mattywausb/lightstick/docs/circuit.jpg

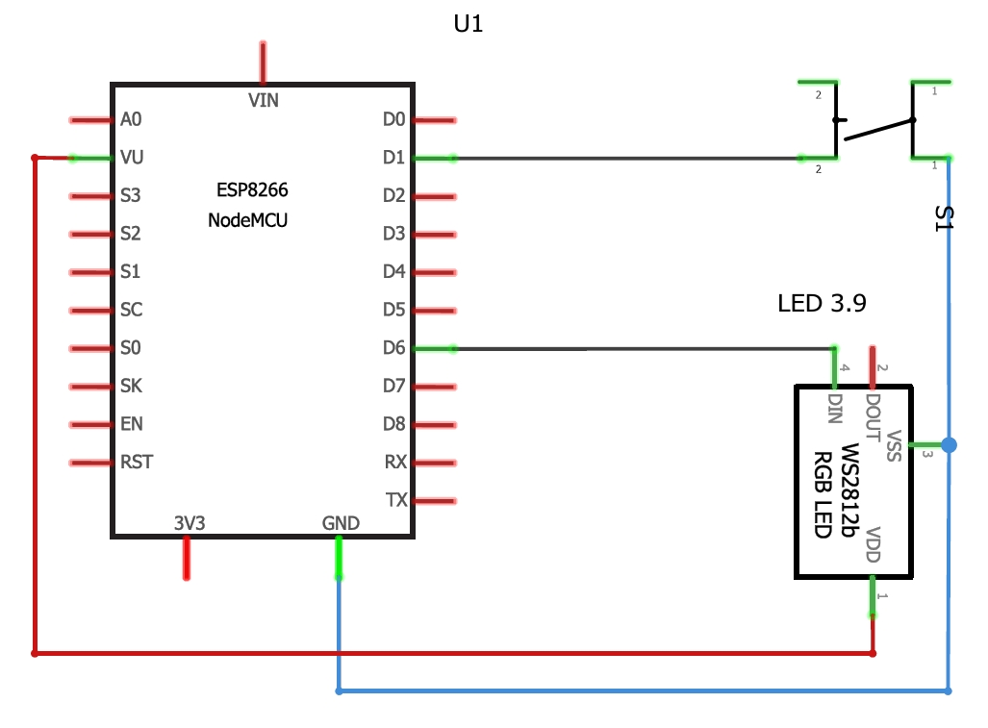
docs/circuit.jpg
