mattywausb/lightstick/docs/D1_mini_pcb_back.jpg

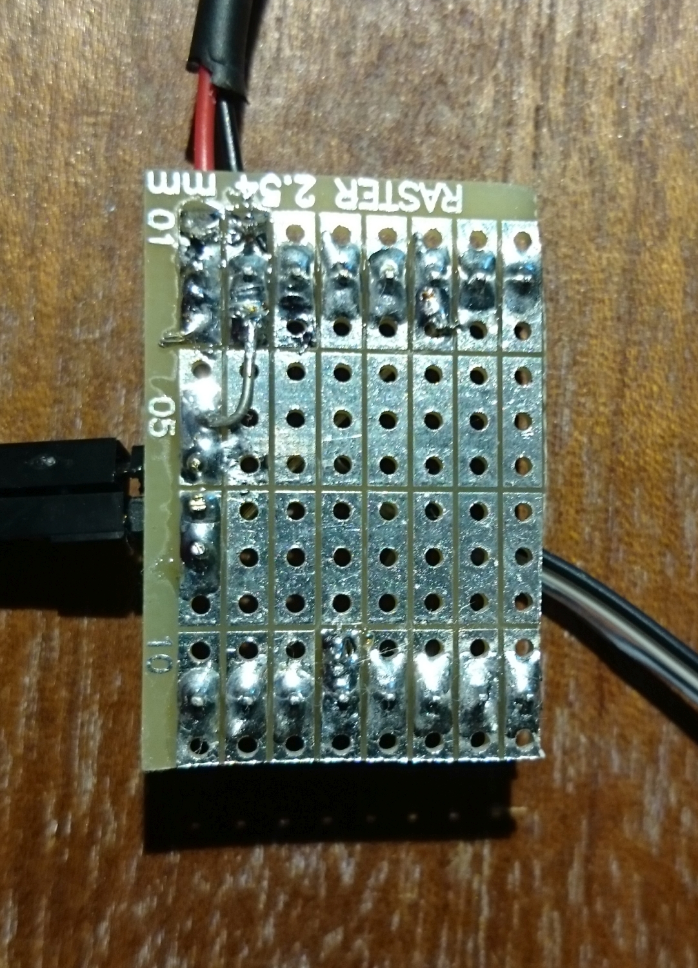
docs/D1_mini_pcb_back.jpg
