mattywausb/lightstick/docs/D1_mini_full_setup.jpg

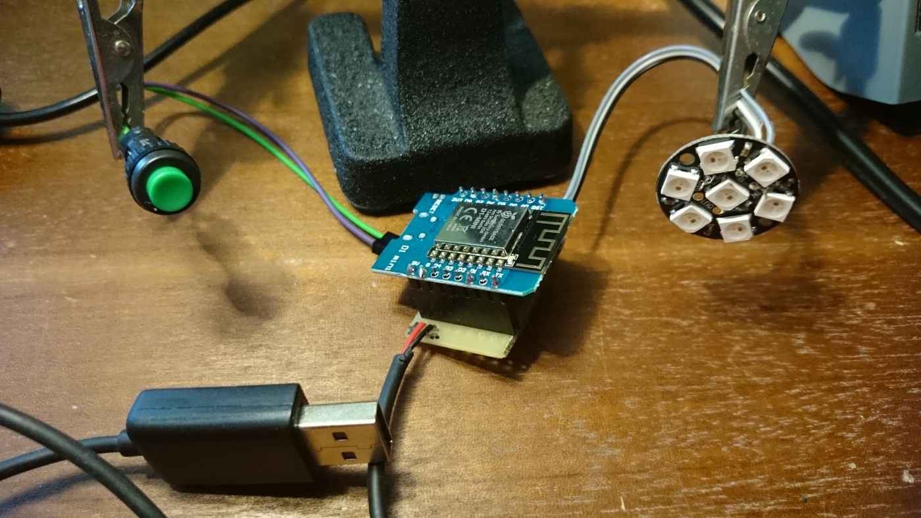
docs/D1_mini_full_setup.jpg
