mattywausb/lightstick/docs/Head_assembly_2.jpg

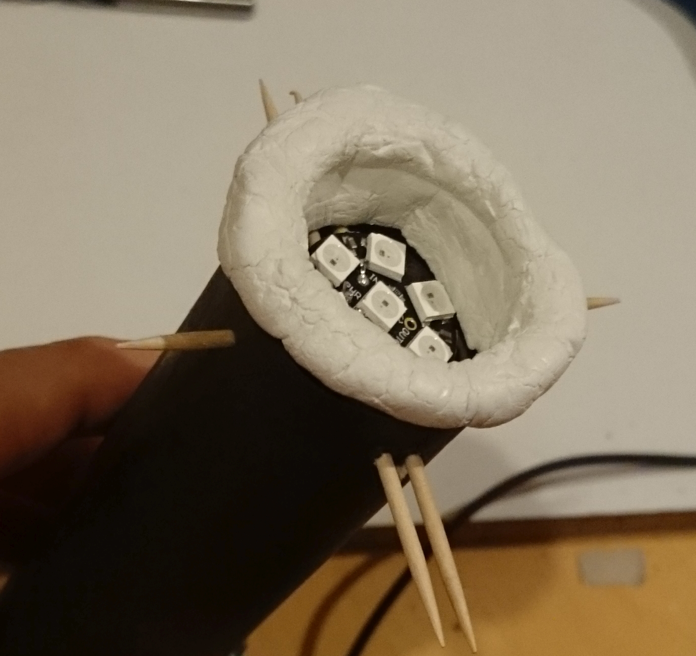
docs/Head_assembly_2.jpg
