mattywausb/lightstick/docs/Head_assembly_3.jpg

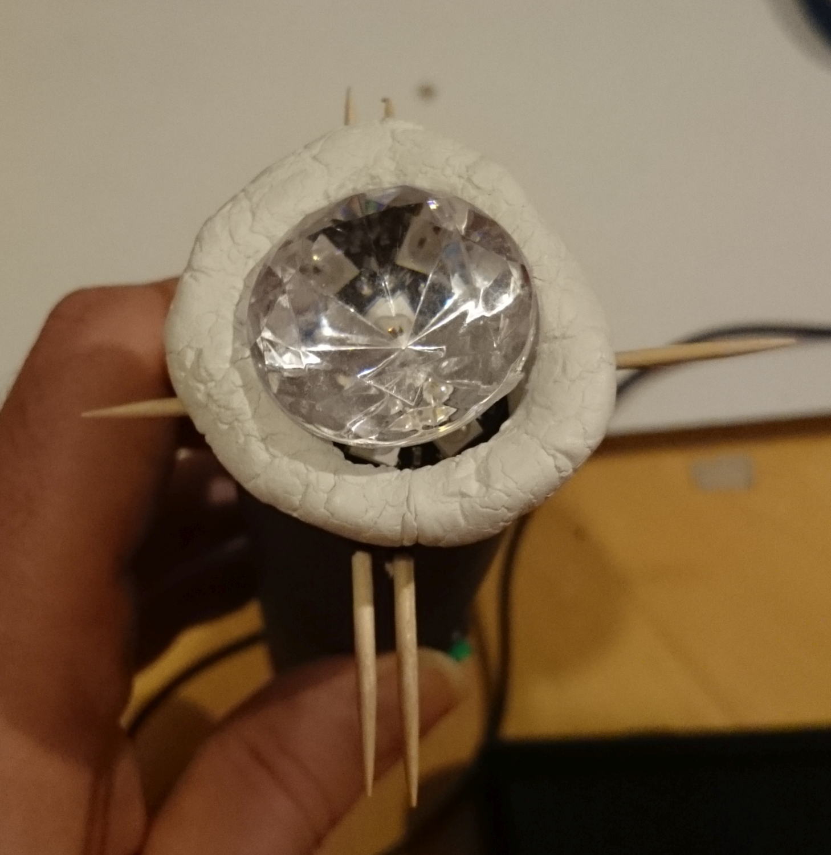
docs/Head_assembly_3.jpg
