mattywausb/lightstick/docs/lightstick_build_schematics.png

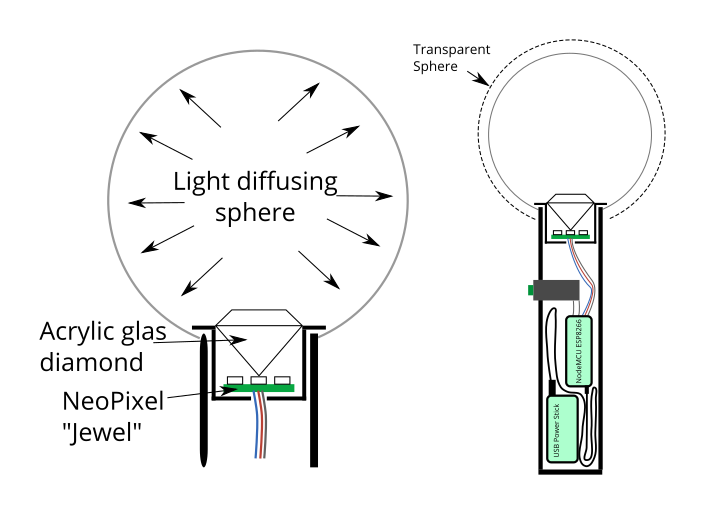
docs/lightstick_build_schematics.png
