mattywausb/lightstick/the_light_stick/webui.ino

/* Compile against  NodeMCU 1.0 Profile */

/*
 * Demonstrate using an http server and an HTML form to control an LED.
 * The http server runs on the ESP8266.
 *
 * Connect to "http://esp8266WebForm.local" or "http://<IP address>"
 * to bring up an HTML form to control the LED connected GPIO#0. This works
 * for the Adafruit ESP8266 HUZZAH but the LED may be on a different pin on
 * other breakout boards.
 *
 * Imperatives to turn the LED on/off using a non-browser http client.
 * For example, using wget.
 * $ wget http://esp8266webform.local/ledon
 * $ wget http://esp8266webform.local/ledoff
*/

#include <ESP8266WiFi.h>
#include <WiFiClient.h>
#include <ESP8266WebServer.h>
#include <ESP8266mDNS.h>
#include "wifi_credentials.h"
#include "webui.h"
#include "mainSettings.h"
#include "lamp.h"

#ifdef TRACE_ON
#define TR_WEBUI
//#define TR_WEBUI_PAGE_GENERATION
#define TR_WEBUI_CONNECT
#endif

/* Macro to declare Strings with reserved buffer */
#define DECLARE_PREALLOCATED_STRING(varname, alloc_size) String varname((const char*)nullptr); varname.reserve(alloc_size)

#define MAX_DEFINITON_STRING_LENGTH 150

//  SSID and password are defined in header file that will not be in the git repo
const char* ssid = STASSID;
const char* password = STAPSK;

String webui_ssid_input="";
String webui_password_input="";
IPAddress webui_ipAddress(0,0,0,0);

t_webui_connect_mode webui_connect_mode =NONE; 

MDNSResponder mdns;

ESP8266WebServer server(80);

String softAp_password="letsparty";

String webui_hostname="lighstick";


/* HTML Header */ 

const char WEB_PAGE_HEADER[] PROGMEM = "<!DOCTYPE html><html>"
"<head> <title>Lightstick</title> "
"<meta http-equiv=\"content-type\" content=\"text/html; charset=utf-8\">"
"<meta name=\"viewport\" content=\"width = device-width, initial-scale = 1.0, maximum-scale = 1.0, user-scalable=0\">"
"<link href=\"default.css\" rel=\"stylesheet\" type=\"text/css\">"
"</head><body>";

const char TXT_CONTENT_TYPE_TEXT_HTML[] PROGMEM = "text/html; charset=utf-8";

void sendStylesheet() {
    #ifdef TR_WEBUI
    Serial.println(F("TR_WEBUI> Sending Stylesheet "));
  #endif
   server.send(200, "text/css", F(
"body{font-family:\"OpenSans\",\"Arial\",\"mono\";color:#f7d53d;background-color:#193c3d;font-size:16px ;text-align:left;}"
"h1{margin:2px 2px ;font-size:18px ;padding:2px 2px ;}"
"label{float:left;margin:2px 2px ;font-size:18px ;padding:2px 2px ;}"
"input[type=\"submit\"]{background-color:#773172;border-radius:4px ;border:none;color:#f7d53d;margin:2px 2px ;padding:16px 16px ;font-size:16px ;cursor:pointer; width:100%}"
"input[type=\"submit\"]:hover{background-color:#a6449f;color:#fff;}"
"input{background-color:#317577;border-radius:4px ;border:none;color:#f7d53d;box-sizing:border-box;margin:2px 2px ;padding:10px 10px ;}"
"select{background-color:#317577;border-radius:4px;border:none;color:#f7d53d;box-sizing:border-box;margin:2px 2px;padding:10px 10px;}"
"textarea{background-color:#317577;border-radius:4px ;border:none;color:#f7d53d;box-sizing:border-box;margin:2px 2px ;padding:10px 10px ;}"
".lb{display:block;background-color:#773172;border-radius:4px ;border:none;color:#f7d53d;padding:10px 10px ;font-size:14px ;cursor:pointer;text-decoration:none}"
".lb:hover{background-color:#a6449f;color:#fff;}"
".lb_box{padding:2px 2px;}"
".anntn{font-size:10px;margin:2px 2px;}"));
}

/* Switchgrid constants */
const char pattx_disco[] PROGMEM ="Disco";
const char pattx_flat[] PROGMEM ="Flat";
const char pattx_orbit[] PROGMEM ="Orbit";
const char pattx_pulse[] PROGMEM ="Pulse";
const char pattx_quater[] PROGMEM ="Quater";
const char pattx_rainbow[] PROGMEM ="Rainbow";
const char pattx_sparkle[] PROGMEM ="Sparkle";
const char pattx_wave[] PROGMEM ="Wave";
const char pattx_whipe[] PROGMEM ="Whipe";

typedef struct pattern_button {
  const char *label;
  int   pattern_id;
  int base_speed;
} t_pattern_button;

t_pattern_button webui_pattern_button[] {
  {pattx_pulse,2,4},    {pattx_whipe,10,4},   {pattx_wave,11,8},
  {pattx_orbit,24,8},   {pattx_disco,44,4},   {pattx_sparkle,104,16},
  {pattx_rainbow,60,16}, {pattx_quater,80,16},  {pattx_flat,90,2}
};

#define WEBUI_PATTERN_BUTTON_COUNT 9


const char coltx_blue[] PROGMEM ="Blue";
const char coltx_cyan[] PROGMEM ="Cyan";
const char coltx_green[] PROGMEM ="Green";
const char coltx_lemon[] PROGMEM ="Lemon";
const char coltx_orange[] PROGMEM ="Orange";
const char coltx_pink[] PROGMEM ="Pink";
const char coltx_purple[] PROGMEM ="Purple";
const char coltx_red[] PROGMEM ="Red";
const char coltx_rose[] PROGMEM ="Rose";
const char coltx_sky[] PROGMEM ="Sky";
const char coltx_white[] PROGMEM ="White";
const char coltx_yellow[] PROGMEM ="Yellow";


typedef struct color_button {
  const char *label;
  int hue;
  float saturation;
} t_color_button;

t_color_button webui_color_button [] {
  {coltx_pink,HUE_PINK,1.0},      {coltx_red,HUE_RED,1.0},    {coltx_orange,HUE_ORANGE,1.0},
  {coltx_yellow, HUE_YELLOW,1.0}, {coltx_lemon,HUE_LEMON,1.0},{coltx_green,HUE_GREEN,1.0} ,
  {coltx_cyan,HUE_CYAN,1.0},      {coltx_sky,HUE_SKYBLUE,1.0},   {coltx_blue,HUE_BLUE,1.0} ,
  {coltx_purple, HUE_PURPLE,1.0} ,{coltx_rose, HUE_RED,SAT_ROSE} ,{coltx_white,HUE_ORANGE,0.0}
};

#define WEBUI_COLOR_BUTTON_COUNT 12




static void send_html_header() {
 
  DECLARE_PREALLOCATED_STRING(s, LARGE_STR);
  s = FPSTR(WEB_PAGE_HEADER);
  server.setContentLength(CONTENT_LENGTH_UNKNOWN);
  server.send(200, FPSTR(TXT_CONTENT_TYPE_TEXT_HTML), s);
}

/* End of Webpage */
const char WEB_PAGE_FOOTER[] PROGMEM = "<hr><div class=\"anntn\">Firmware Build " __DATE__ " " __TIME__ "</div> </body></html>\r\n";


static void send_html_footer() {
  server.sendContent_P(WEB_PAGE_FOOTER);
  #ifdef TR_WEBUI
    Serial.println(F("TR_WEBUI> Page sent "));
  #endif
      
}

const char WEB_PAGE_BUTTON_TABLE_START[] PROGMEM =
      "<div>" 
      "<table width=100%>";
      
const char WEB_PAGE_PATTERN_PART_HEADING[] PROGMEM =
      "<tr>"
      "<td><h1>Pattern</h1></td>"
      "</tr>"; 

const char WEB_PAGE_COLOR_PART_HEADING[] PROGMEM =
      "<tr>"
      "<td><h1>Color<h1></td>"
      "</tr>"; 

const char WEB_PAGE_BUTTON_TABLE_END[] PROGMEM = "</table></div>";


const char WEB_PAGE_FORM_SECTION_START[] PROGMEM ="<hr/><div><form id=\"progform\" action=\"/#progform\" method=\"post\">"; 

const char WEB_PAGE_SEQ_PART_START[] PROGMEM =
      "<div> <label for=\"Sequence\" >Song Sequence</label>"
      "<textarea  id=\"Sequence\" name=\"Sequence\" style=\"width:100%; height:3;\" >";
  

const char WEB_PAGE_SEQ_PART_END[] PROGMEM =
      "</textarea> </div>"
      "<div class=\"anntn\">"
      "Syntax: &lt;bpm&gt; &lt;Part Letter&gt; &lt;Beats&gt;&lt;Beats&gt;... &lt;Part Letter&gt;...<br/>"
      "# = Forward immediatly to next on button press <br/>"
      "&gt; = Jump back here after end<br/>"
      "Part Letter is defined in Song part configuration<br/>"
      "Beats are one digit numbers, that get accumulated: 8888=32 Beats <br/>"
      "248 =14 Beats"
      "</div>";

const char WEB_PAGE_SONG_PART_START[] PROGMEM =
      "<div > <label for=\"Parts\" >Song Parts</label>"
      "<textarea  id=\"Parts\" name=\"Parts\" style=\"width:100%; height:1; \" >";

const char WEB_PAGE_SONG_PART_END[] PROGMEM =
      "</textarea> </div>"
      "<div class=\"anntn\">"
      "Syntax:  &lt;Part Letter&gt;&lt;Pattern&gt;/&lt;Speed&gt;:&lt;color&gt;... <br/>"
      "Pattern: identifies the pattern of light change (see pattern catalog)<br/>"
      "Speed: Speed of the pattern 2=Haft Beat 4=Beat 8=8th, 16,32,64 <br/>"
      "Color: defines the color palette (see color catalog)"
      "</div>";

const char WEB_PAGE_FORM_END[] PROGMEM =
      "<input type=\"submit\" value=\"Start\">"
      "</form>";

const char WEB_PRESET_SECTION_START[] PROGMEM =
      "<hr/>"
      "<h1 id=\"presets\">Song Presets</h1>";

const char WEB_FILEFORM_P1[] PROGMEM =
      "<hr/>"
      "<form id=\"fileform\" action=\"#fileform\" method=\"post\">"
      "<table width=100%>"
      "<tr><td><label for=\"filename\" >Filename</label>"
      "<input type=\"text\" id=\"filename\" name=\"filename\" value=\"";
      // Insert Filename here
const char WEB_FILEFORM_P2[] PROGMEM =
      "\">"
      "</td><td><label for=\"file-op\">Operation</label>"
      "<select id=\"file-op\" name=\"file-op\">"
        "<option value=\"cre\">create</option>"
        "<option value=\"upd\">update</option>"
        "<option value=\"del\">delete</option>"
      "</select>"
      "</td><td ><div style=\"color:#ff0000\" ><b>";
      // Insert catalog message here
const char WEB_FILEFORM_P3[] PROGMEM =
      "</b></div>"
      "</td></tr></table>"
      "<input type=\"submit\" value=\"Execute\">"
      "</form>";

const char WEB_WIFI_P1[] PROGMEM =
          "<hr/>"
          "<h1>Wifi Settings</h1>"
          "<form action=\"/\" method=\"post\">"
          "<table><tr>"
          "<td><label for=\"SSID\" class=\"col-1\">SSID</label>"
          "<input type=\"text\" id=\"SSID\" name=\"SSID\" value=\"";
          // Insert SSID String 
const char WEB_WIFI_P2[] PROGMEM =
          "\"></td>"
          "<td><label for=\"Password\" class=\"col-1\">Password</label>"
          "<input type=\"text\" id=\"WIFIPW\" name=\"WIFIPW\" value=\"";
          // Insert wifi password here
const char WEB_WIFI_P3[] PROGMEM =
        "\" autocomplete=\"off\" autocapitalize=\"off\" autocorrect=\"off\"></td>"
         "</table></tr>"
        "<div class=\"anntn\" >"
        "To try out the credentials, the stick will disconnect and this website will not be available any more. When successfull, access the stick in the target network. In case of blue light, connect to the sticks own wifi to access it"
        "</div>"
        "<input type=\"submit\" value=\"connect to wifi\">"
        "</form>";

         
      

void send_main_page() {

  #ifdef TR_WEBUI
   Serial.println(F("TR_WEBUI> send_main_page started"));
  #endif
  
  String local_buffer_string;
  
  send_html_header() ;

  char string_buffer[MAX_DEFINITON_STRING_LENGTH];
  
  DECLARE_PREALLOCATED_STRING(content_element,XLARGE_STR);
  
  // *******************  Button Grid ***************************
  server.sendContent_P(WEB_PAGE_BUTTON_TABLE_START);

  // -------------- Pattern Buttons ------------------------
  #ifdef TR_WEBUI_PAGE_GENERATION
   Serial.println(F("TR_WEBUI_PAGE_GENERATION> render pattern buttons"));
  #endif
    server.sendContent_P(WEB_PAGE_PATTERN_PART_HEADING);
    for(int element_index=0;element_index<WEBUI_PATTERN_BUTTON_COUNT;element_index++) {
        if(element_index%3==0) content_element+="<tr>"; 

        content_element+=F("<td><div class=\"lb_box\"><a class=\"lb\"  href=\"/switch?p=");
        content_element+=webui_pattern_button[element_index].pattern_id;
        content_element+=F("&w=");
        content_element+=webui_pattern_button[element_index].base_speed;
        content_element+=("\">");
        strcpy_P(string_buffer, (char*)pgm_read_dword(&(webui_pattern_button[element_index].label)));
        content_element+=string_buffer;
        content_element+=F("</a></div></td>");
    
        content_element+=F("<td><div class=\"lb_box\"><a class=\"lb\"  href=\"/switch?p=");
        content_element+=webui_pattern_button[element_index].pattern_id;
        content_element+=F("&w=");
        content_element+=webui_pattern_button[element_index].base_speed*4;
        content_element+=("\">&gt;&gt;");
        content_element+=F("</a></div></td>");
        if(element_index%3==2) content_element+="</tr>";  // Works only for button count  that is dividable by 3
   } // end loop over all Pattern Buttons
   server.sendContent(content_element);
   content_element="";
   
  // -------------- color Buttons ------------------------
  #ifdef TR_WEBUI_PAGE_GENERATION
   Serial.println(F("TR_WEBUI_PAGE_GENERATION> render color buttons"));
  #endif
    server.sendContent_P(WEB_PAGE_COLOR_PART_HEADING);
    
    for(int element_index=0;element_index<WEBUI_COLOR_BUTTON_COUNT;element_index++) {
        if(element_index%3==0) content_element+="<tr>"; // 3 Column format
        content_element+=F("<td><div class=\"lb_box\"><a class=\"lb\"  href=\"/switch?i=1&h=");
        content_element+=webui_color_button[element_index].hue;
        content_element+=F("&s=");
        content_element+=webui_color_button[element_index].saturation;
        content_element+="\">";
        strcpy_P(string_buffer, (char*)pgm_read_dword(&(webui_color_button[element_index].label)));
        content_element+=string_buffer;
        content_element+=F("</a></div></td>");
        content_element+=F("<td><div class=\"lb_box\"><a class=\"lb\"  href=\"/switch?h=");
        content_element+=webui_color_button[element_index].hue;
        content_element+=F("&s=");
        content_element+=webui_color_button[element_index].saturation;
        content_element+="\">+";
        content_element+=F("</a></div></td>");
        if(element_index%3==2) content_element+="</tr>";  // Works only for button count that is dividable by 3
      }
   server.sendContent(content_element);
   content_element="";
   server.sendContent_P(WEB_PAGE_BUTTON_TABLE_END);
 
  // *******************Song catalog ****************
  #ifdef TR_WEBUI_PAGE_GENERATION
   Serial.println(F("TR_WEBUI_PAGE_GENERATION> render song preset buttons"));
  #endif
 
  server.sendContent_P(WEB_PRESET_SECTION_START);
  song_catalog_goto_start();
  while(song_catalog_next()) {
        local_buffer_string=song_catalog_list_name;
        local_buffer_string.replace(" ","_");
        content_element+=F("<div class=\"lb_box\"><a class=\"lb\"  href=\"song?song_name=");
        content_element+=(local_buffer_string);  
        content_element+=F("#presets\">");
        content_element+=song_catalog_list_name;
        content_element+=F("</a></div>");
  } // Loop over song catalog

  /*Now get it all out to the user */
  server.sendContent(content_element);

  // ******************* Send Sequence Section Form ****************
  #ifdef TR_WEBUI_PAGE_GENERATION
   Serial.println(F("TR_WEBUI_PAGE_GENERATION> render seqence entry form"));
  #endif
  
  server.sendContent_P(WEB_PAGE_FORM_SECTION_START);

  // Parts
  server.sendContent_P(WEB_PAGE_SONG_PART_START);
  if(song_catalog_current_parts.length()>0) server.sendContent(song_catalog_current_parts);
  server.sendContent_P(WEB_PAGE_SONG_PART_END);

  // Sequence
  server.sendContent_P(WEB_PAGE_SEQ_PART_START);
  if(song_catalog_current_sequence.length()>0) server.sendContent(song_catalog_current_sequence);
  server.sendContent_P(WEB_PAGE_SEQ_PART_END);
  
  // End of Part/ Sequence Form
  server.sendContent_P(WEB_PAGE_FORM_END);

  // ******************* Send file management form ****************
  #ifdef TR_WEBUI_PAGE_GENERATION
   Serial.println(F("TR_WEBUI_PAGE_GENERATION> render file management form"));
  #endif

  server.sendContent_P(WEB_FILEFORM_P1);
  if(song_catalog_current_name.length()>0) server.sendContent(song_catalog_current_name);
  server.sendContent_P(WEB_FILEFORM_P2);
  if(song_catalog_status_message.length()>0) server.sendContent(song_catalog_status_message);
  song_catalog_status_message="";
  server.sendContent_P(WEB_FILEFORM_P3);

  // ******************* Wifi connect form ****************
  #ifdef TR_WEBUI_PAGE_GENERATION
   Serial.println(F("TR_WEBUI_PAGE_GENERATION> render wifi connect form"));
  #endif

  server.sendContent_P(WEB_WIFI_P1);
  if(webui_ssid_input.length()>0) server.sendContent(webui_ssid_input);
  server.sendContent_P(WEB_WIFI_P2);
  if(webui_password_input.length()>0) server.sendContent(webui_password_input);
  server.sendContent_P(WEB_WIFI_P3);
 
  // ******************* finally  ****************
  #ifdef TR_WEBUI_PAGE_GENERATION
   Serial.println(F("TR_WEBUI_PAGE_GENERATION> html render complete"));
  #endif
  send_html_footer();
}

// ************* Request management FORMS ****************************

void receiveSongConfigForm()
{
  #ifdef TR_WEBUI
    Serial.println(F("TR_WEBUI> receiveSongConfigForm started"));
  #endif
  if (server.hasArg("Parts")) {
      song_catalog_current_parts = server.arg("Parts");
  }

  if (server.hasArg("Sequence")) {
      song_catalog_current_sequence = server.arg("Sequence");
  }
  parse_slot_settings( song_catalog_current_parts);
  parse_sequence (song_catalog_current_sequence);
}

void receiveFileOperationForm()
{
  #ifdef TR_WEBUI
    Serial.println(F("TR_WEBUI> receiveFileOperationForm started"));
  #endif

  String file_name;
  String file_operation;
   
  if (server.hasArg("filename")) {
     file_name=server.arg("filename");
     file_operation=server.arg("file-op");
     #ifdef TR_WEBUI
      Serial.print(F("TR_WEBUI> file-op"));Serial.println(file_operation);
     #endif
     if(file_operation=="del") {
        song_catalog_delete_song(file_name);
     } else {
       song_catalog_save_song(file_name, file_operation=="upd");
     }
  }
  #ifdef TR_WEBUI
      else  Serial.print(F("TR_WEBUI> error:"));Serial.println(song_catalog_status_message);
  #endif   
}

void receiveWifiConnectForm()
{
  #ifdef TR_WEBUI
    Serial.println(F("TR_WEBUI> receiveWifiConnectForm started"));
  #endif
  if (server.hasArg("SSID")) {
      webui_ssid_input = server.arg("SSID");
  }

  if (server.hasArg("WIFIPW")) {
      webui_password_input = server.arg("WIFIPW");
  }
  webui_change_wifi(); 
}

// ************* Request management URLS ****************************

void handleRoot()
{
  #ifdef TR_WEBUI
    Serial.println(F("TR_WEBUI> handleRoot started"));
  #endif
  if (server.hasArg("Parts")) {
    receiveSongConfigForm();
  }
  if (server.hasArg("filename")) {
    receiveFileOperationForm();
  }
  if (server.hasArg("SSID")) {
     receiveWifiConnectForm();
  }
  send_main_page() ;
}

void handleSong()
{
  #ifdef TR_WEBUI
    Serial.println(F("TR_WEBUI> handleSong started"));
  #endif

  String song_name;
   
  if (server.hasArg("song_name")) {
     song_name=server.arg("song_name");
     song_name.replace("_"," ");  // Revert the tagging
     #ifdef TR_WEBUI
       Serial.print(F("TR_WEBUI> song_name:"));Serial.println(song_name);
    #endif   
    if(song_catalog_load_song(song_name)) {
      parse_slot_settings( song_catalog_current_parts);
      parse_sequence (song_catalog_current_sequence);
    } 
  #ifdef TR_WEBUI
      else  Serial.print(F("TR_WEBUI> error:"));Serial.println(song_catalog_status_message);
  #endif   
  }
  send_main_page() ;
}



void handleSwitch()
{
  #ifdef TR_WEBUI
    Serial.println(F("TR_WEBUI> handleSwitch started"));
  #endif
  String url_parameter_value;
  if (server.hasArg("p")) {  // Pattern switch
    url_parameter_value=server.arg("p");
    output_start_pattern(url_parameter_value.toInt());
    mode_of_operation=MODE_FIX_PRESET;
  }
  if (server.hasArg("w")) {  // Pattern switch
    url_parameter_value=server.arg("w");
    int preset_speed_id=preset_speed_to_id(server.arg("w"));
    if(preset_speed_id>=0)output_set_pattern_speed(preset_speed_id);
    mode_of_operation=MODE_FIX_PRESET;
  }
  if (server.hasArg("h")&&server.hasArg("s")) {
    float hue = server.arg("h").toFloat();
    float saturation = server.arg("s").toFloat();
    if(server.hasArg("i")) output_reset_color_palette(hue,saturation);
    else output_add_color_palette_entry(hue,saturation);
    mode_of_operation=MODE_FIX_PRESET;
  }
  send_main_page() ;
}

// ************* Request management standards ****************************

void returnFail(String msg)
{
  server.sendHeader("Connection", "close");
  server.sendHeader("Access-Control-Allow-Origin", "*");
  server.send(500, "text/plain", msg + "\r\n");
}


void returnOK()
{
  server.sendHeader("Connection", "close");
  server.sendHeader("Access-Control-Allow-Origin", "*");
  server.send(200, "text/plain", "OK\r\n");
}

void handleNotFound()
{
  String message = "Not a valid request\n";
  message += "URI: ";
  message += server.uri();
  message += "\nMethod: ";
  message += (server.method() == HTTP_GET)?"GET":"POST";
  message += "\nArguments: ";
  message += server.args();
  message += "\n";
  for (uint8_t i=0; i<server.args(); i++){
    message += " " + server.argName(i) + ": " + server.arg(i) + "\n";
  }
  //message += "<a href=\"/\">Get Back to start</a>\n";
  server.send(404, "text/plain", message);
}

// ************************* Network Management *******************************************

// Setup return code will connection result
// 1 = Couldconncet to WiFi
// 2 = Started own AP
// 0 = no WiFi available

t_webui_connect_mode webui_setup(boolean force_softAP) {

    // Esatblish all url handlers
    server.on("/", handleRoot); // manages all forms
    server.on("/song", handleSong);
    server.on("/switch", handleSwitch);
    server.on("/default.css", sendStylesheet);
    server.onNotFound(handleNotFound);

    // Start Network
    webui_hostname="Lightstick-"+String(ESP.getChipId());
    WiFi.hostname(webui_hostname);   
     
    if(force_softAP) {
      establish_soft_AP();
    } else webui_connect_wifi();
    
    if(webui_connect_mode!=NONE){
         webui_start_services();
         webui_initiate_adress_pattern();
    } else {
         webui_initiate_nowifi_pattern();
    }
   
    #ifdef TRACE_ON
    Serial.println(F(">webui_setup finished "));
    #endif
    return webui_connect_mode;
}

void establish_soft_AP() {
    String ap_ssid=webui_hostname+"-AP";
    webui_ipAddress=IPAddress(192,168,4,10);
    IPAddress gateway(192,168,4,254);
    IPAddress subnet(255,255,255,0);
    if(!WiFi.softAPConfig(webui_ipAddress, gateway, subnet)) {
       #ifdef TR_WARNING
          Serial.println("\n#!# TR_WARNING> Could not configure SoftAP ");
       #endif;
    }
    if(WiFi.softAP(ap_ssid,softAp_password)) {
        IPAddress myIP = WiFi.softAPIP();
        webui_connect_mode =SOFT_AP;
        #ifdef TR_WEBUI_CONNECT
          Serial.print("\nTR_WEBUI_CONNECT>Started access point:'"+ap_ssid+"' password:'"+softAp_password+"' with IP ");
          Serial.println(myIP);
        #endif
     } else {
       webui_connect_mode =NONE;
       #ifdef TR_WARNING
          Serial.println("\n#!# TR_WARNING> Could not start any Wifi ");
       #endif
     }
}

void webui_change_wifi() {
    webui_stop_services();
    
    webui_connect_wifi();

    if(webui_connect_mode!=NONE){
         webui_start_services();
         webui_initiate_adress_pattern();
    } else {
         webui_initiate_nowifi_pattern();
    }
}

void webui_start_services() {
         #ifdef TR_WEBUI_CONNECT
           Serial.print("TR_WEBUI_CONNECT> Hostname: ");    Serial.println(webui_hostname);
           Serial.print("TR_WEBUI_CONNECT> IP address: ");    Serial.println(webui_ipAddress);
         #endif 
         
         if (mdns.begin(webui_hostname,webui_ipAddress)) {
           Serial.println("TR_WEBUI_CONNECT> MDNS responder started");
         }
         server.begin();
         #ifdef TR_WEBUI_CONNECT
          Serial.println("TR_WEBUI_CONNECT> Webserver started ");
         #endif 
}

void webui_stop_services() {
    #ifdef TR_WEBUI_CONNECT
           Serial.println("TR_WEBUI_CONNECT> Stopping Services");    
    #endif
    server.stop();
    mdns.end();
}

t_webui_connect_mode webui_connect_wifi()
{
  if(WiFi.status() == WL_CONNECTED ) WiFi.disconnect();  
  webui_connect_mode =NONE; 
  
  if(webui_ssid_input.length()>0) { // try to use the given credentials
    WiFi.begin(webui_ssid_input, webui_password_input);
    #ifdef TR_WEBUI_CONNECT
      Serial.print("TR_WEBUI_CONNECT> Try to connect to "); Serial.println(webui_ssid_input);
    #endif 
  } else {    
      WiFi.begin();
      #ifdef TR_WEBUI_CONNECT
        Serial.print("TR_WEBUI_CONNECT> Try to connect last Access Point:");
        Serial.println(WiFi.SSID());
      #endif 
  }

  for(int retry=0; WiFi.status() != WL_CONNECTED && retry<15; retry++) {
      #ifdef TR_WEBUI_CONNECT
         Serial.print('.');
      #endif
      delay(500);
  } 
    
  if(WiFi.status() == WL_CONNECTED)  webui_connect_mode =WIFI;
  else { 
     WiFi.begin(ssid, password);
    #ifdef TR_WEBUI_CONNECT
      Serial.print("TR_WEBUI_CONNECT> Try to connect to default SSID ");
      Serial.println(ssid);
    #endif 
    for(int retry=0; WiFi.status() != WL_CONNECTED && retry<10; retry++) {
      #ifdef TR_WEBUI_CONNECT
         Serial.print('.');
      #endif
      delay(500);
    }
     if(WiFi.status() == WL_CONNECTED)  webui_connect_mode =WIFI;
  } 

  webui_ipAddress=WiFi.localIP();
  if(WiFi.status() != WL_CONNECTED) establish_soft_AP();

  return webui_connect_mode;
}

void webui_initiate_adress_pattern(){
  
String adress_string=(webui_ipAddress[0]) + String(".") +\
  String(webui_ipAddress[1]) + String(".") +\
  String(webui_ipAddress[2]) + String(".") +\
  String(webui_ipAddress[3])  ;

  mode_of_operation=MODE_FIX_PRESET;
  output_set_bpm(80);
  output_set_pattern_speed(STEP_ON_8TH);
  String part_description ="F8/4:19999 P8/4:29999 A20/4:10000 B20/4:12222 C20/4:16666 Z11/4:19999 ";
  String sequence_description = "100 I8 P2 ";

  // Example F8/4:19999 P8/4:29999 A20/4:10000 B20/4:12222 C20/4:16666 I8/4:17777   
  // Example 100 I8 P2 A1 F2 B9 F2 C2 F2 P2 A1 F2 B6 F2 C8 F2 P2 A1 F2 B7 F2 C8 F2 P2 A8 F2 B3 F2 
  //                    !     !     !        !     !     !        !     !     !        !     !
  //                    1     9     2    .   1     6     8     .  1     7     8    .   8     3   
  
  switch (webui_connect_mode) {
    case WIFI: part_description += "I8/4:14444";
               break;
    case SOFT_AP: part_description += "I8/4:17777";
               break;
  }

  int digit=0;
  char pattern_letter='A';
  for(int i=0;i<adress_string.length();i++) {
    if(adress_string[i]=='.') {
      sequence_description +="P2 ";
      pattern_letter='A';
    }
    else {
      if(adress_string[i]!='0') sequence_description +=String(pattern_letter)+String(adress_string[i])+" F2 ";
      else sequence_description += "Z2 F2 ";
      pattern_letter++;
    }   
  }

  parse_slot_settings(part_description);
  parse_sequence (sequence_description);
}


void webui_initiate_nowifi_pattern() {
  mode_of_operation=MODE_FIX_PRESET;
  output_set_bpm(80);
  output_set_pattern_speed(STEP_ON_BEAT);
  output_reset_color_palette(HUE_RED,1);
  output_start_pattern(9);  // Heartbeat with low light
};


void webui_loop(void)
{
  server.handleClient();
  yield();
}
