mattywausb/lightstick/LightShow_preparation/output.h

#ifndef __OUTPUT_H__
#define __OUTPUT_H__
#define STEP_ON_2BEATS 0
#define STEP_ON_BEAT   1
#define STEP_ON_8TH    2
#define STEP_ON_16TH   3
#define STEP_ON_32RD   4
#define STEP_ON_64TH   5

#define PROGRAM_TAG_OFF '-'
#endif
